Ghanshyam1409/PCB-Design-of-Flyback-Converter-/ou.png

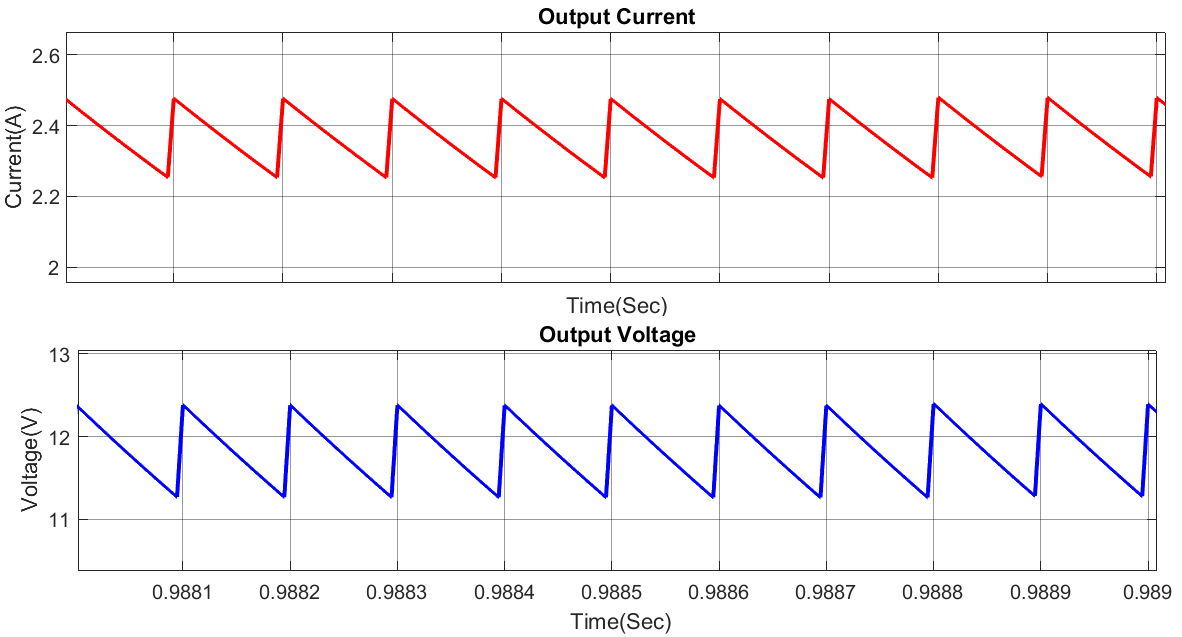
ou.png
