Ghanshyam1409/PCB-Design-of-Flyback-Converter-/sw.png

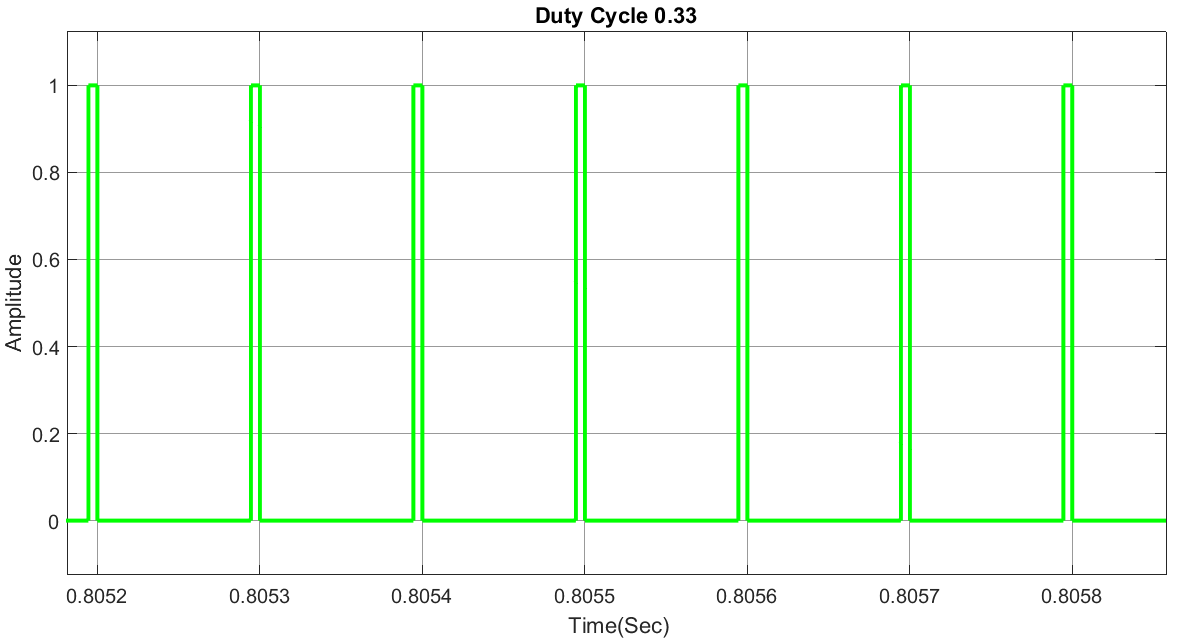
sw.png
