Ghanshyam1409/PCB-Design-of-Flyback-Converter-/totalcom.png

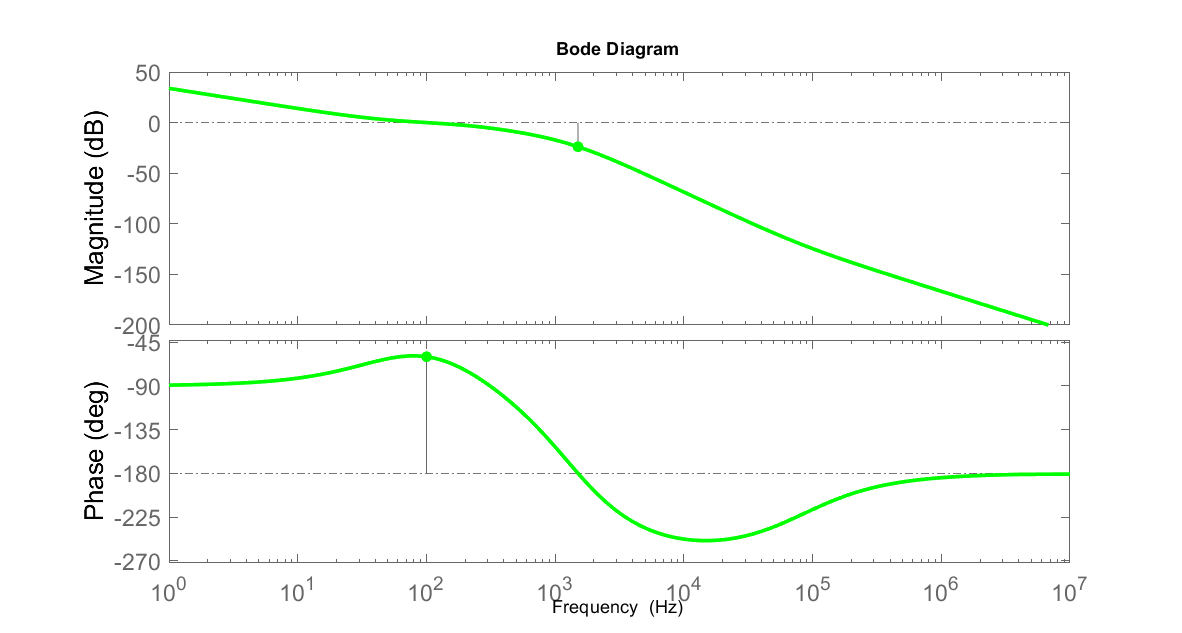
totalcom.png
