Ghanshyam1409/PCB-Design-of-Flyback-Converter-/uncom.png

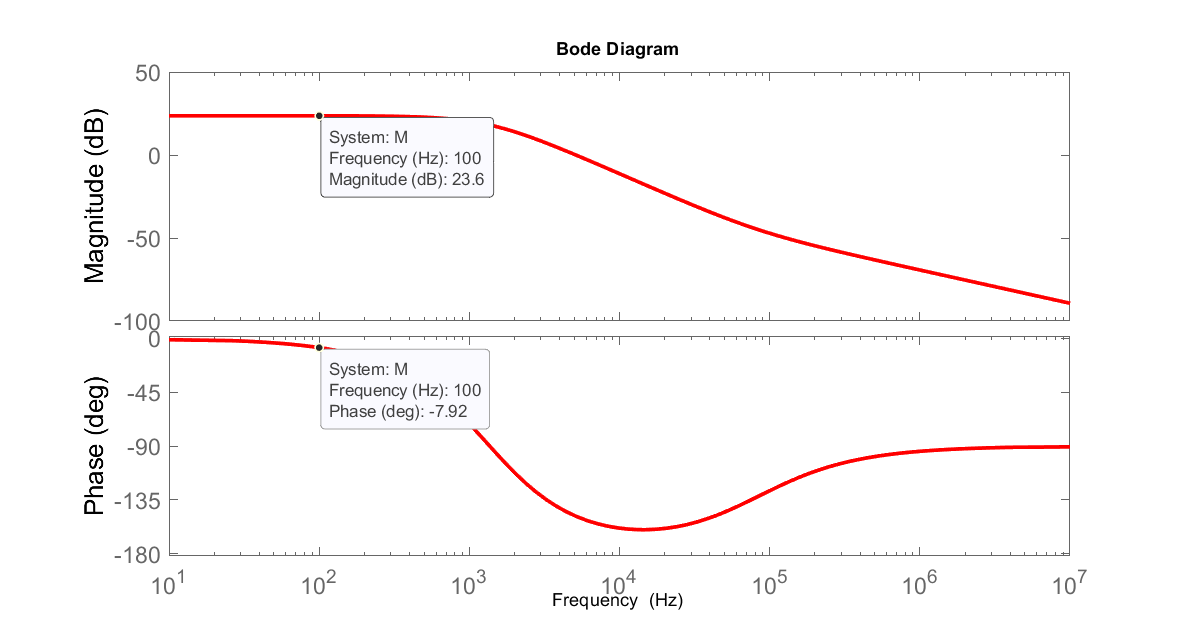
uncom.png
